YWonchall/fire_alarm_device/images/image9.png

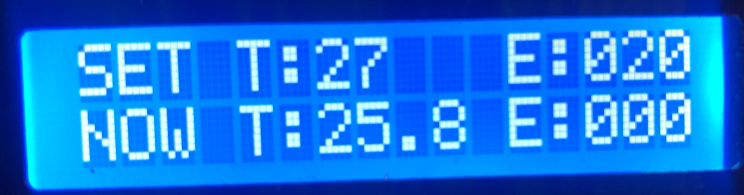
images/image9.png
